akira215/zVMC/3Dprint/screenshot/Slicer params.png

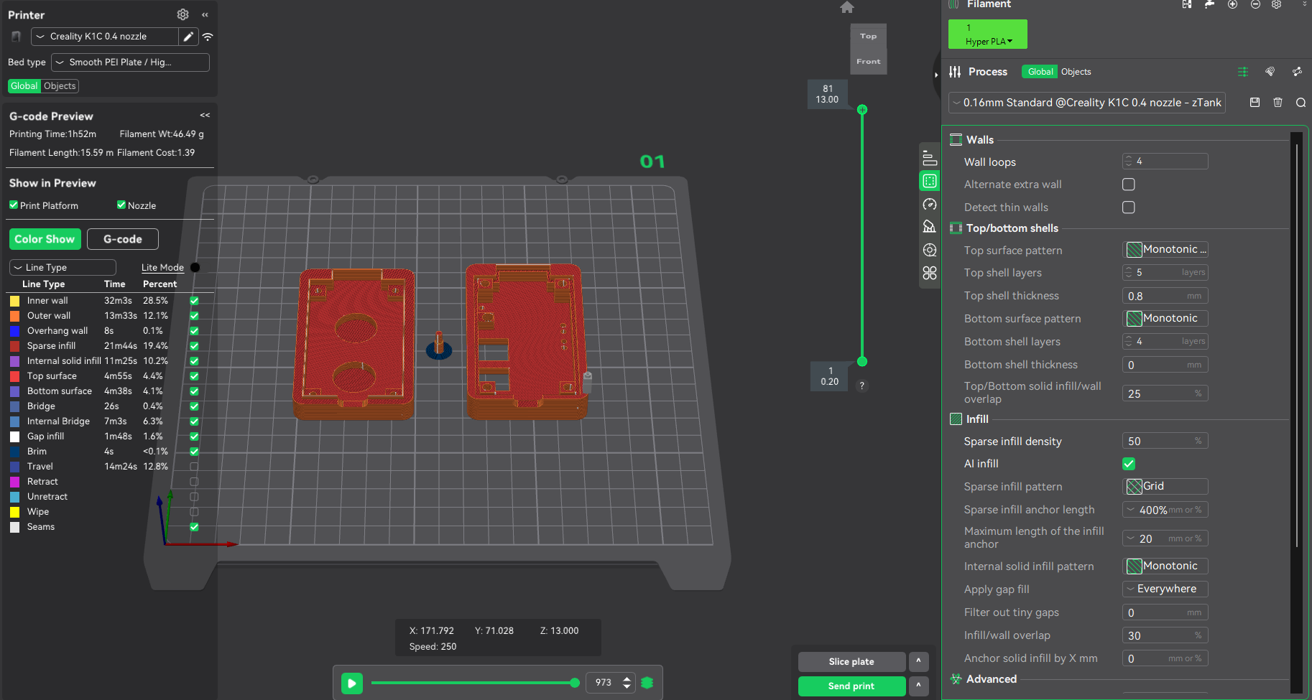
3Dprint/screenshot/Slicer params.png
