akira215/zVMC/PCB/screenshot/zTankV1_1 iso-r.png

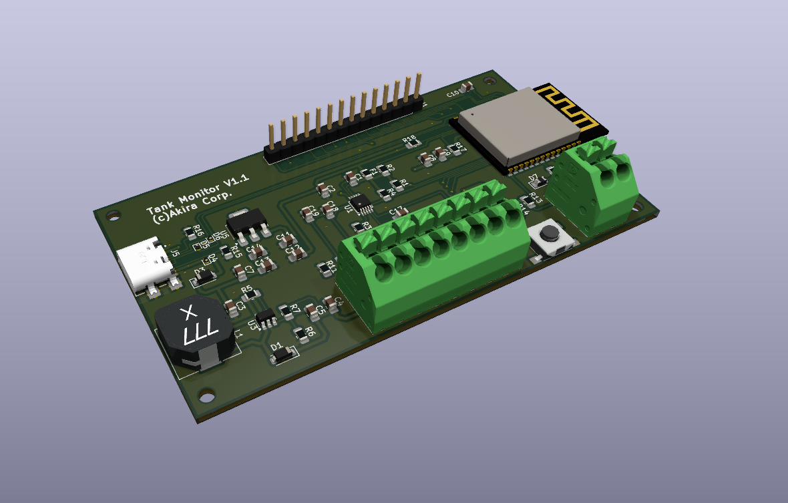
PCB/screenshot/zTankV1_1 iso-r.png
