akira215/zVMC/PCB/screenshot/zTankV1_1 top-ortho.png

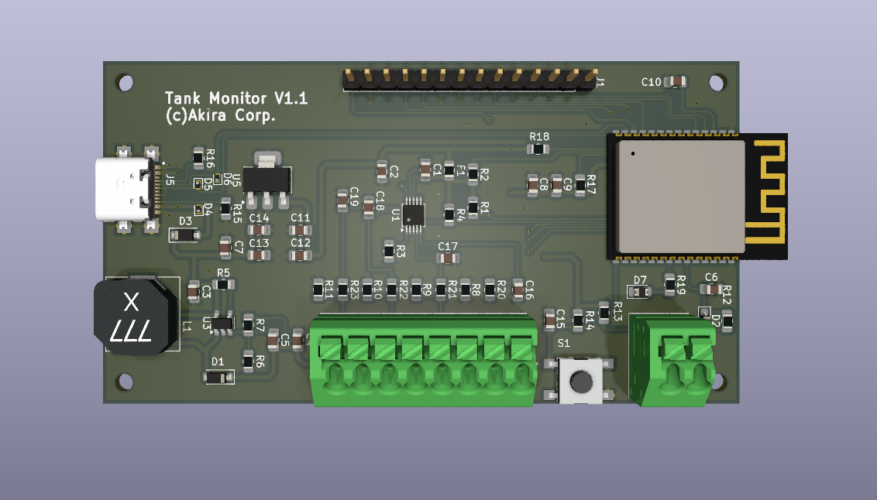
PCB/screenshot/zTankV1_1 top-ortho.png
