akira215/zVMC/PCB/screenshot/zTankV1_1 top-parall wb.png

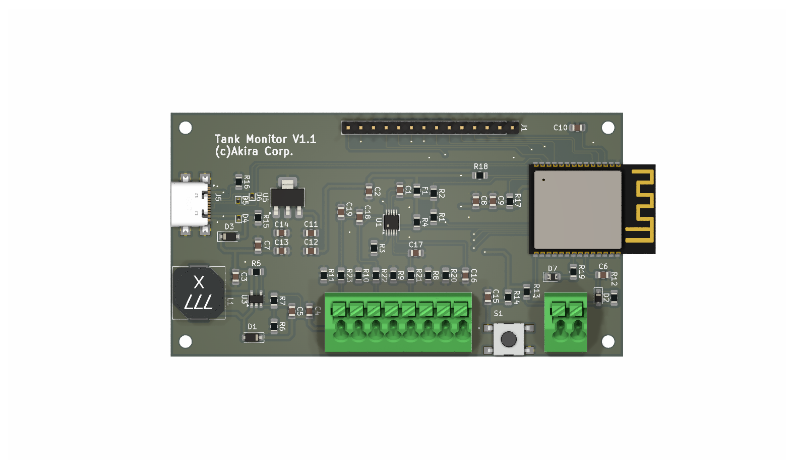
PCB/screenshot/zTankV1_1 top-parall wb.png
