akira215/zVMC/main/main.h

#pragma once

#include "zbNode.h"
#include "cppgpio.h" // to del
#include "buttonTask.h" // to del
#include "blinkTask.h" // to del

#include "aldesDriver.h"

#include "tSensorCluster.h"
#include "filterTimerCluster.h"
#include "bypassCluster.h"
#include "setPointCluster.h" 
#include "airflowCluster.h"
#include "flowSettingsCluster.h" 

#include "zbOtaClusterClient.h"

#include "zbHaCluster.h"
#include "zbTimeClusterClient.h" 


/* Attribute values in ZCL string format
 * The string should be started with the length of its own.
 */
#define MANUFACTURER_NAME               "\x09""AkiraCorp" //TODO del
#define MODEL_IDENTIFIER                "\x10""AldesMonitor"  //TODO del


// Main class used for testing only
class Main final
{
    GpioInput               _button {(gpio_num_t)CONFIG_PIN_BUTTON, true};
    ButtonTask*             _buttonTask = nullptr;

    static BlinkTask*       _ledBlinking;
    static GpioOutput       _led;
    
    // As hardware is planned for 2 uart, configure 2nd uart pin as input and output
    GpioOutput              _tx1 {(gpio_num_t)10};
    GpioInput               _rx1 {(gpio_num_t)11};
    GpioOutput              _rts1 {(gpio_num_t)1};

public:
    Main();
    void run(void);
    void setup(void);

    void zbDeviceEventHandler(ZbNode::nodeEvent_t event);
    static void shortPressHandler(void *handler_args, esp_event_base_t base, int32_t id, void *event_data);
    static void longPressHandler(void *handler_args, esp_event_base_t base, int32_t id, void *event_data);

    static void identifyHandler(uint16_t attrId, void* value);

private:
    /// @brief Helper to flash led
    /// @param speed flash cycle in ms. if 0, led will be set to off, 
    /// if -1 led will be switch on
    static void ledFlash(uint64_t speed);
    
    // Check RTC Sync and trigger all operation that require to be RTC sync
    void checkRTCSync();

    ZbNode*                     _zbDevice           = nullptr;
    ZbTimeClusterClient*        _timeClient         = nullptr;

    TaskHandle_t                _xButtonHandle      = nullptr;
    TaskHandle_t                _eventLoopHandle    = nullptr;
    TaskHandle_t                _mbHandle           = nullptr;

    TSensorCluster*             _TIntakeOut         = nullptr;
    TSensorCluster*             _TExtractIn         = nullptr;
    TSensorCluster*             _TSupplyIn          = nullptr;
    TSensorCluster*             _TExhaustOut        = nullptr;

    FilterTimerCluster*         _filterTimerCluster = nullptr;
    BypassCluster*              _tBypassCluster     = nullptr;
    SetPointCluster*            _setPointCluster    = nullptr;
    AirflowCluster*             _airflowMVECluster  = nullptr;
    AirflowCluster*             _airflowMVICluster  = nullptr;

    FlowSettingsCluster*        _flowSettingsCluster = nullptr;

    ZbOtaClusterClient*         _otaCluster         = nullptr;

    PeriodicSoftTask*           _checkRTCSync       = nullptr;

    AldesDriver*                _aldes              = nullptr;        

}; // Main Class
